knovvX/TECHIN514_Project/514_display/test 3d print/514_display v7upup.stl

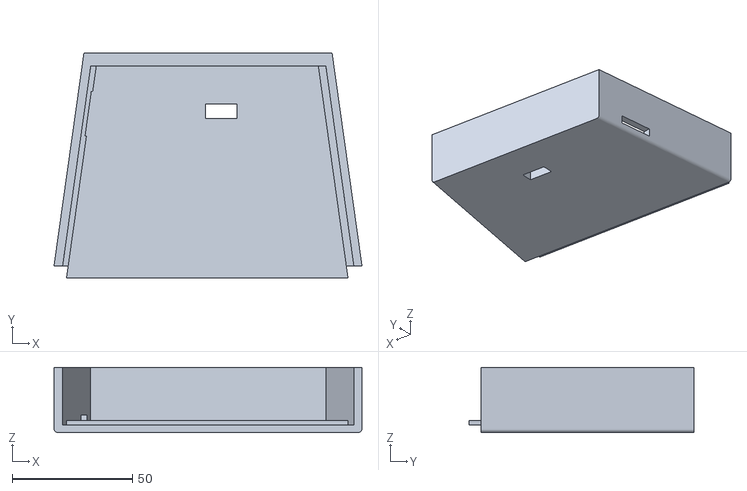
[picture p20: CAD file, 2025-03-12]
514_display/test 3d print/514_display v7upup.stl
128.0 x 93.4 x 27.0
