knovvX/TECHIN514_Project/514_display/test 3d print/514_display v5 bot.stl

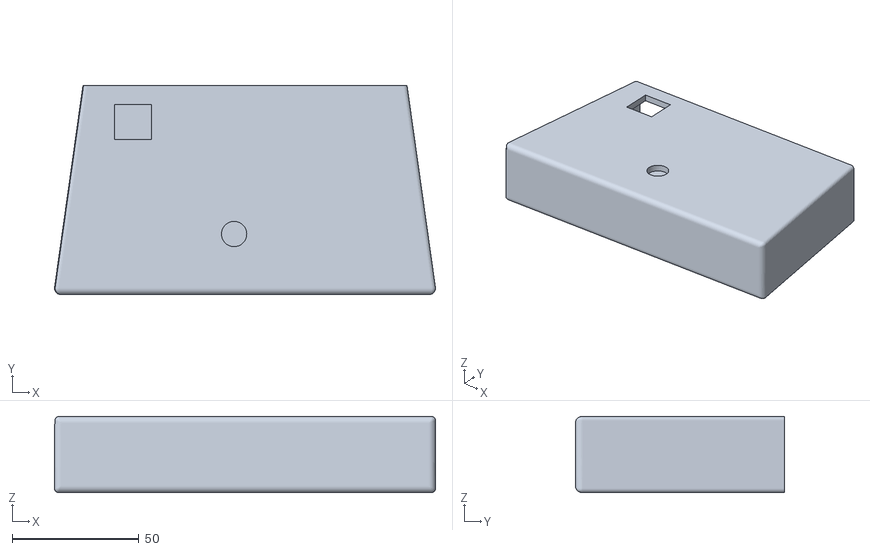
[picture p21: CAD file, 2025-03-12]
514_display/test 3d print/514_display v5 bot.stl
150.5 x 82.6 x 30.0
