knovvX/TECHIN514_Project/514_display/test 3d print/514_display v7need1.stl

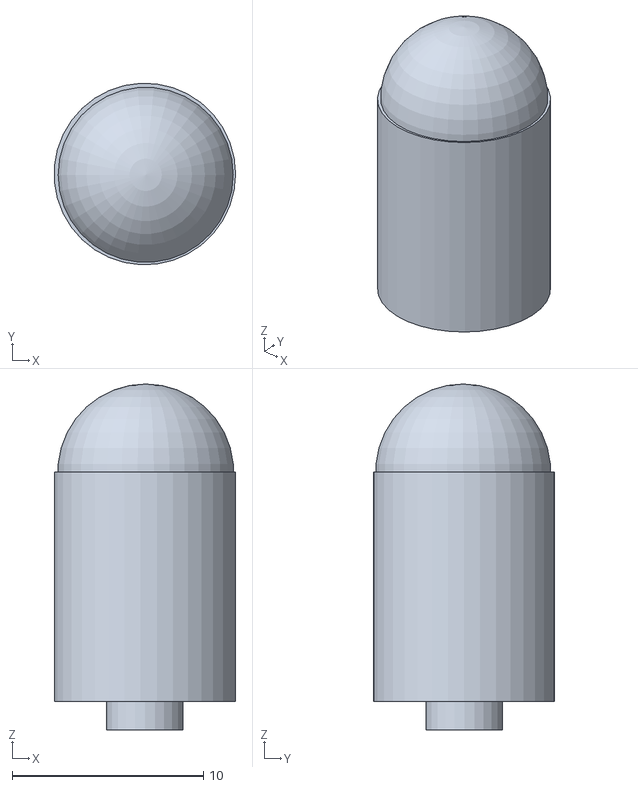
[picture p22: CAD file, 2025-03-12]
514_display/test 3d print/514_display v7need1.stl
9.48 x 9.49 x 18.1
