knovvX/TECHIN514_Project/514_display/test 3d print/514_display v5 up1.stl

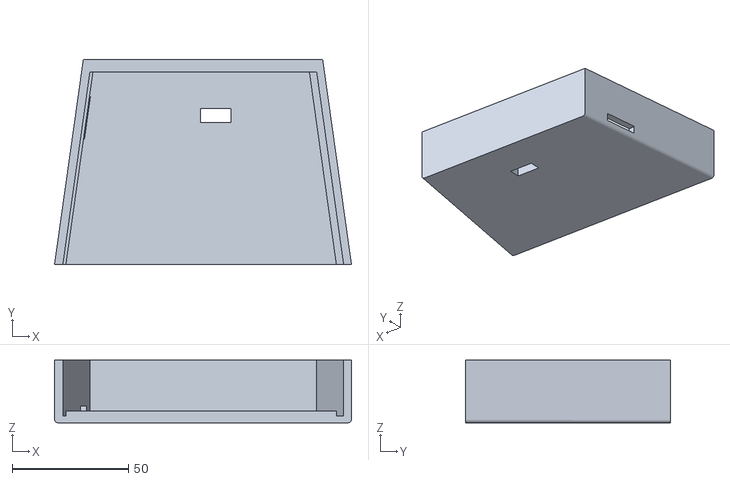
[picture p23: CAD file, 2025-03-12]
514_display/test 3d print/514_display v5 up1.stl
128.0 x 88.4 x 27.0
