knovvX/TECHIN514_Project/514_display/test 3d print/514_display v2 upbot.stl

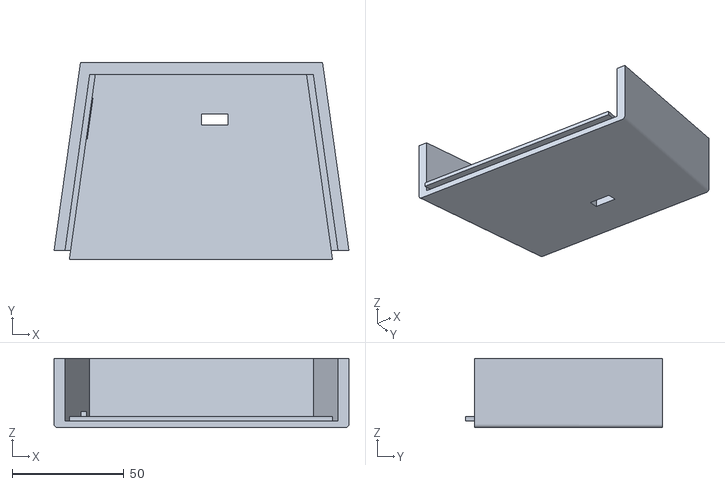
[picture p24: CAD file, 2025-03-12]
514_display/test 3d print/514_display v2 upbot.stl
132.2 x 88.4 x 31.1
