knovvX/TECHIN514_Project/514_display/test 3d print/514_display v7botup.stl

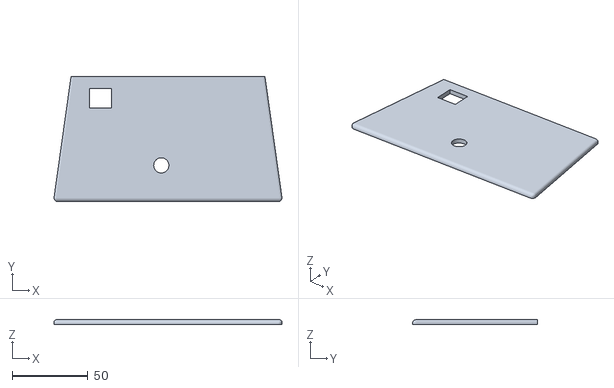
[picture p25: CAD file, 2025-03-12]
514_display/test 3d print/514_display v7botup.stl
150.2 x 82.6 x 3.02
