knovvX/TECHIN514_Project/514_display/test 3d print/514_display v5up2.stl

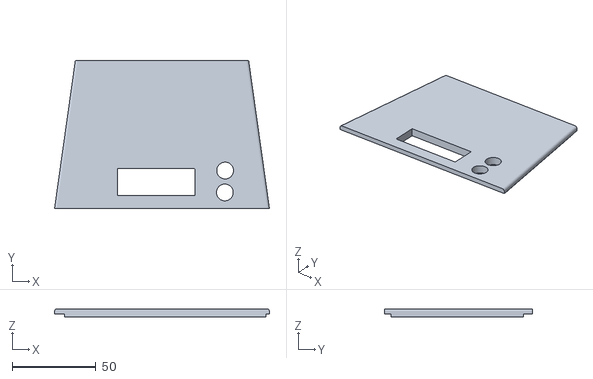
[picture p26: CAD file, 2025-03-12]
514_display/test 3d print/514_display v5up2.stl
128.0 x 88.4 x 5.02
