knovvX/TECHIN514_Project/514_display/test 3d print/ldy_test_up2.stl

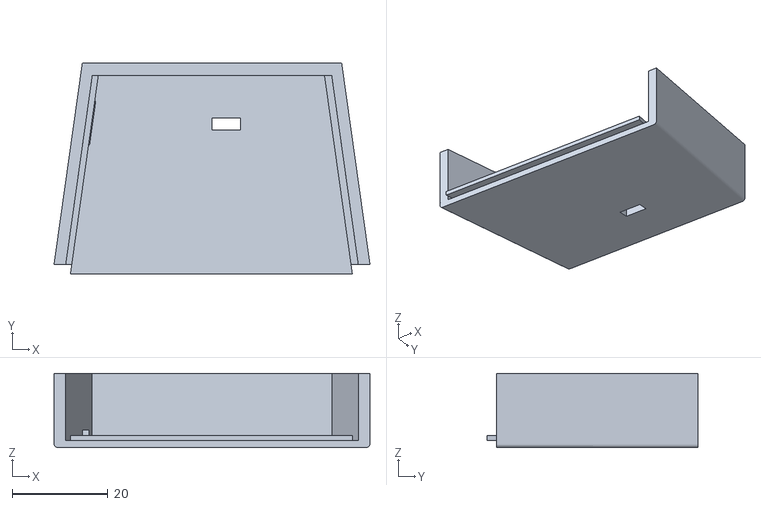
[picture p27: CAD file, 2025-03-12]
514_display/test 3d print/ldy_test_up2.stl
66.1 x 44.2 x 15.5
