knovvX/TECHIN514_Project/514_display/test 3d print/ldy_test_up1.stl

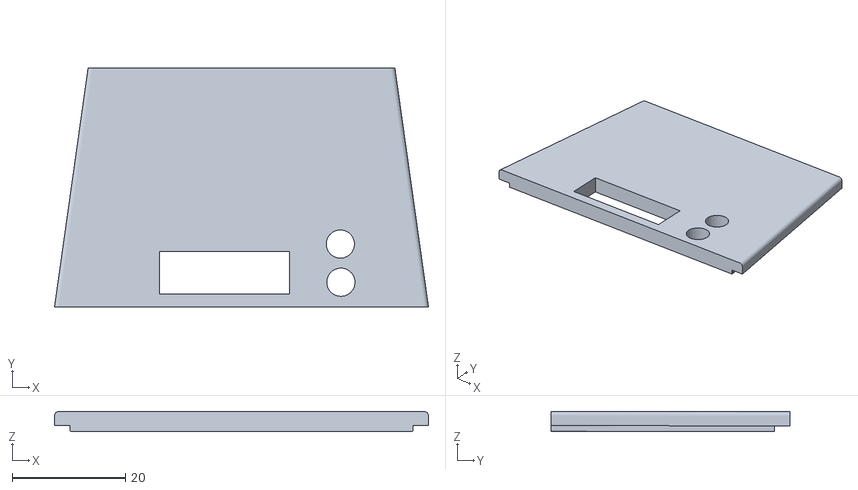
[picture p28: CAD file, 2025-03-12]
514_display/test 3d print/ldy_test_up1.stl
66.1 x 42.2 x 3.54
