knovvX/TECHIN514_Project/514_display/test 3d print/514_display_down.stl

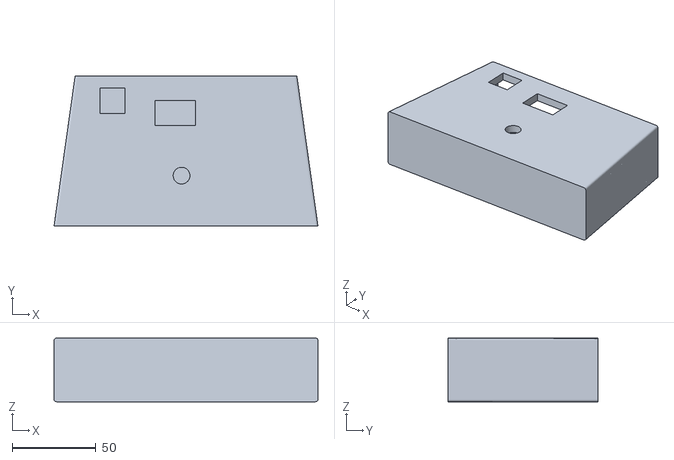
[picture p29: CAD file, 2025-03-04]
514_display/test 3d print/514_display_down.stl
157.4 x 89.6 x 38.1
