knovvX/TECHIN514_Project/514_display/test 3d print/514_display v1.stl

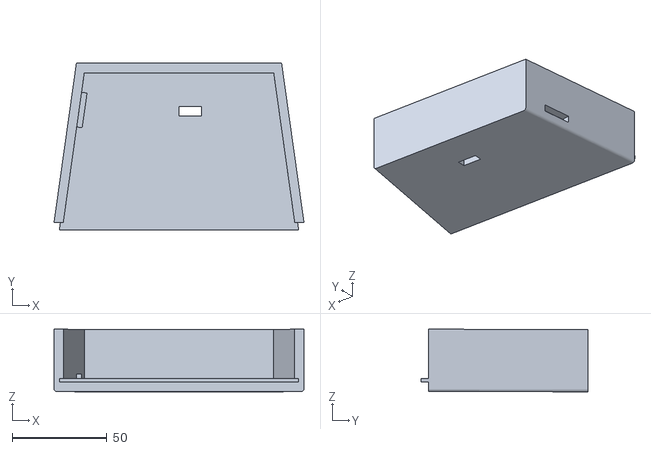
[picture p30: CAD file, 2025-03-04]
514_display/test 3d print/514_display v1.stl
132.2 x 88.4 x 33.1
