knovvX/TECHIN514_Project/514_display/test 3d print/514_display upup.stl

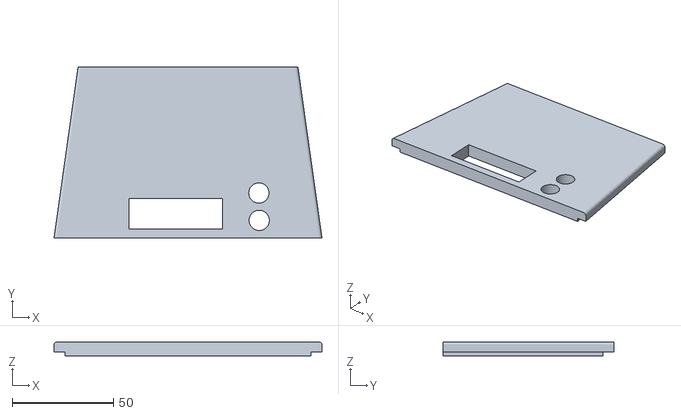
[picture p31: CAD file, 2025-03-04]
514_display/test 3d print/514_display upup.stl
132.2 x 84.4 x 7.09
