knovvX/TECHIN514_Project/Arduio Test Codes/test_microphone_ble/test_microphone_ble.ino

#include <ESP_I2S.h>
#include <BLEDevice.h>
#include <BLEServer.h>
#include <BLEUtils.h>
#include <BLE2902.h>

I2SClass I2S;

// BLE server and characteristic definitions
BLEServer *pServer = NULL;
BLECharacteristic *pCharacteristic = NULL;
bool deviceConnected = false;
bool oldDeviceConnected = false;

// Define UUIDs for the service and characteristic
#define SERVICE_UUID "0cebcba9-4624-4999-9cec-5debf01d8ecb"
#define CHARACTERISTIC_UUID "65f04fbf-01ac-4954-a999-af6b77c65fdf"
// Buffer for audio data
int16_t sampleBuffer[64];
int bufferIndex = 0;

// Server callbacks class to detect connection status
class MyServerCallbacks: public BLEServerCallbacks {
    void onConnect(BLEServer* pServer) {
      deviceConnected = true;
      Serial.println("Device connected");
    }

    void onDisconnect(BLEServer* pServer) {
      deviceConnected = false;
      Serial.println("Device disconnected");
    }
};

void setup() {
  // Open serial communications and wait for port to open:
  // A baud rate of 115200 is used instead of 9600 for a faster data rate
  // on non-native USB ports
  Serial.begin(115200);
  while (!Serial) {
    ; // wait for serial port to connect. Needed for native USB port only
  }

  // setup 42 PDM clock and 41 PDM data pins
  I2S.setPinsPdmRx(42, 41);
  
  // start I2S at 16 kHz with 16-bits per sample
  if (!I2S.begin(I2S_MODE_PDM_RX, 16000, I2S_DATA_BIT_WIDTH_16BIT, I2S_SLOT_MODE_MONO)) {
    Serial.println("Failed to initialize I2S!");
    while (1); // do nothing
  }

  // Initialize BLE
  Serial.println("Starting BLE work!");
  
  BLEDevice::init("ESP32_I2S_MIC");
  
  // Create the BLE Server
  pServer = BLEDevice::createServer();
  pServer->setCallbacks(new MyServerCallbacks());
  
  // Create the BLE Service
  BLEService *pService = pServer->createService(SERVICE_UUID);
  
  // Create a BLE Characteristic
  pCharacteristic = pService->createCharacteristic(
                      CHARACTERISTIC_UUID,
                      BLECharacteristic::PROPERTY_READ   |
                      BLECharacteristic::PROPERTY_WRITE  |
                      BLECharacteristic::PROPERTY_NOTIFY |
                      BLECharacteristic::PROPERTY_INDICATE
                    );
  
  // Create a BLE Descriptor
  pCharacteristic->addDescriptor(new BLE2902());
  
  // Start the service
  pService->start();
  
  // Start advertising
  BLEAdvertising *pAdvertising = BLEDevice::getAdvertising();
  pAdvertising->addServiceUUID(SERVICE_UUID);
  pAdvertising->setScanResponse(true);
  pAdvertising->setMinPreferred(0x06);
  pAdvertising->setMinPreferred(0x12);
  BLEDevice::startAdvertising();
  
  Serial.println("BLE device is ready to pair");
}

void loop() {
  // Read a sample from I2S
  int sample = I2S.read();
  
  if (sample && sample != -1 && sample != 1) {
    // Print sample to serial for debugging
    // Serial.println(sample);
    
    // If BLE is connected, add sample to buffer
    if (deviceConnected) {
      sampleBuffer[bufferIndex] = (int16_t)sample;
      bufferIndex++;
      
      // When buffer is full, send data over BLE
      if (bufferIndex >= 64) {
        // We can't send the entire buffer at once because BLE packets are limited in size
        // Typically 20 bytes per packet, so we send 10 samples (20 bytes) at a time
        for (int i = 0; i < 64; i += 10) {
          pCharacteristic->setValue((uint8_t*)&sampleBuffer[i], 20); // 10 samples * 2 bytes per sample
          pCharacteristic->notify();
          delay(10); // Small delay to avoid overwhelming the BLE stack
        }
        
        bufferIndex = 0;
      }
    }
  }
  
  // Disconnection handling
  if (!deviceConnected && oldDeviceConnected) {
    delay(500); // Give the bluetooth stack time to get ready
    pServer->startAdvertising(); // Restart advertising
    Serial.println("Started advertising again");
    oldDeviceConnected = deviceConnected;
  }
  
  // Connection handling
  if (deviceConnected && !oldDeviceConnected) {
    oldDeviceConnected = deviceConnected;
  }
}
